KennethWang1/snakez80/loader/rom.hpp

PROGMEM const char FULL_CODE[1340] = "\x31\0\x08\xc3\xd7\x03\0\0\0\0\0\0\0\0\0\0\0\0\0\0\0\0\0\0\0\0\0\0\0\0\0\0\0\0\0\0\0\0\0\0\0\0\0\0\0\0\0\0\0\0\0\0\0\0\0\0\0\0\0\0\0\0\0\0\0\0\0\0\0\0\0\0\0\0\0\0\0\0\0\0\0\0\0\0\0\0\0\0\0\0\0\0\0\0\0\0\0\0\0\0\0\0\0\0\0\0\0\0\0\0\0\0\0\0\0\0\0\0\0\0\0\0\0\0\0\0\0\0\0\0\0\0\0\0\0\0\0\0\0\0\0\0\0\0\0\0\0\0\0\0\0\0\0\0\0\0\0\0\0\0\0\0\0\0\0\0\0\0\0\0\0\0\0\0\0\0\0\0\0\0\0\0\0\0\0\0\0\0\0\0\0\0\0\0\0\0\0\0\0\0\0\0\0\0\0\0\0\0\0\0\0\0\0\0\0\0\0\0\0\0\0\0\0\0\0\0\0\0\0\0\0\0\0\0\0\0\0\0\0\0\0\0\0\0\0\0\0\0\0\0\0\0\0\0\0\0\0\0\0\0\0\0\0\0\0\0\0\0\x21\0\x80\x4e\xaf\xb9\x17\x6f\xc9\x2a\x01\x80\xc9\xdd\xe5\xdd\x21\0\0\xdd\x39\x21\0\x80\xdd\x7e\x04\x77\xdd\xe1\xc9\x21\x01\x80\x36\0\xc9\xdd\xe5\xdd\x21\0\0\xdd\x39\x21\x07\x80\xdd\x7e\x04\x77\xdd\xe1\xc9\x2a\x32\x04\x5d\x54\xaf\xcb\x3c\xcb\x1d\x1f\x65\x6f\xeb\x7d\xab\x47\x7c\xaa\x4f\xcb\x3f\x5f\x78\xab\x6f\x61\x29\x29\x29\xad\x6f\x79\xac\x67\x22\x32\x04\xc9\x76\xc9\xdd\xe5\xdd\x21\0\0\xdd\x39\x21\xf2\xff\x39\xf9\x06\x80\x21\x0c\0\xaf\x77\x23\x77\x23\x10\xf9\x3a\x39\x04\x06\0\xdd\x77\xfe\xdd\x70\xff\x21\x3a\x04\x86\xdd\x77\xfc\x78\x23\x8e\xdd\x77\xfd\xdd\x7e\xfe\xdd\x96\xfc\xdd\x7e\xff\xdd\x9e\xfd\xe2\xae\x01\xee\x80\xf2\xd6\x01\xdd\x6e\xfe\x26\0\x11\x3c\x04\x19\x6e\x26\0\x11\x0c\0\x19\x7e\xb7\x28\x05\x3e\x01\x32\x35\x04\x36\x02\xdd\x34\xfe\x20\xcc\xdd\x34\xff\x18\xc7\x0e\0\x79\x21\x34\x04\x96\x30\x12\x06\0\x21\x06\0\x09\x6e\x26\0\x11\x0c\0\x19\x36\x03\x0c\x18\xe7\x21\x35\x04\xcb\x46\xca\x7d\x02\xdd\x36\xf2\xc1\xdd\x36\xf3\xce\xdd\x36\xf4\xaa\xdd\x36\xf5\xa8\xdd\x36\xf6\xa2\xdd\x36\xf7\xac\xdd\x36\xf8\xaa\xdd\x36\xf9\xa8\xdd\x36\xfa\xc1\xdd\x36\xfb\xce\x01\0\0\x79\xd6\x05\x30\x54\x69\x60\x29\xeb\x21\0\0\x39\x19\x7e\xdd\x77\xfc\x23\x7e\xdd\x77\xfd\x21\x06\0\x09\x29\x29\x29\x29\xdd\x75\xfe\xdd\x74\xff\x11\0\0\x7b\xd6\x10\x30\x29\x6b\x3e\x0f\x95\xdd\x6e\xfc\xdd\x66\xfd\x3c\x18\x04\xcb\x3c\xcb\x1d\x3d\x20\xf9\xcb\x45\x28\x0e\xdd\x7e\xfe\xb3\x62\xc6\x0c\x6f\x7c\xce\0\x67\x36\x01\x13\x18\xd2\x03\x18\xa7\x01\0\0\x78\xd6\x01\x30\x0b\x21\x0c\0\x09\x7e\x32\0\x80\x03\x18\xf0\xdd\xf9\xdd\xe1\xc9\x3a\0\x80\xb7\x28\x57\x3a\x37\x04\xd6\x02\x20\x04\x21\x37\x04\x35\x3a\x37\x04\x4f\xaf\x91\x30\x19\x06\0\x21\x0a\0\x09\x79\x3d\x47\x07\x9f\x57\x78\xc6\x0a\x5f\x7a\xce\0\x57\x1a\x77\x0d\x18\xe3\x21\x37\x04\x34\x3a\x01\x80\xe6\x03\x6f\x26\0\x11\x2d\x04\x19\x7e\x32\x0a\0\x4f\x07\x9f\x47\x21\x32\x04\x7e\xa9\x77\x23\x7e\xa8\x77\xcd\x43\x01\xcd\x43\x01\xc3\x43\x01\xc9\xdd\xe5\xdd\x21\0\0\xdd\x39\xf5\xf5\x21\x37\x04\x7e\xb7\x28\x25\x4e\x0d\x71\x06\0\x21\x0a\0\x09\x4e\x3a\x36\x04\x47\x07\x9f\x57\xaf\x90\x5f\x9f\x92\x57\x79\x6f\x07\x9f\x67\xaf\xed\x52\x28\x04\x21\x36\x04\x71\x01\x3c\x04\x2a\x39\x04\x26\0\x09\x66\x3a\x36\x04\x6f\xeb\x07\x9f\x6f\x7a\x26\0\x83\xdd\x77\xfc\x7c\x8d\xdd\x77\xfd\x3a\x36\x04\xdd\x5e\xfc\x0f\x30\x1a\x6b\xcb\x3d\xcb\x3d\xcb\x3d\xcb\x3d\x7a\x07\x07\x07\x07\xe6\x0f\x95\x28\x12\x21\x35\x04\x36\x01\x18\x0b\xdd\x7e\xfd\xb7\x28\x05\x21\x35\x04\x36\x01\x21\x35\x04\xcb\x46\x20\x56\x21\x39\x04\x35\x79\x86\x4f\x30\x01\x04\x7b\x02\x01\0\0\x3a\x34\x04\x5f\x16\0\x79\x93\x78\x9a\xe2\x9a\x03\xee\x80\xf2\xd2\x03\x21\x06\0\x09\xdd\x75\xfe\xdd\x74\xff\x5e\x16\0\xe1\xe5\xaf\xed\x52\x20\x1e\x2a\x3a\x04\x23\x22\x3a\x04\xc5\xcd\x43\x01\xeb\xc1\x16\0\x21\x0c\0\x19\x7e\xb7\x20\xf0\xdd\x6e\xfe\xdd\x66\xff\x73\x03\x18\xb9\xdd\xf9\xdd\xe1\xc9\x06\x80\x21\x0c\0\xaf\x77\x23\x77\x23\x10\xf9\x01\0\0\x3a\x34\x04\x5f\x16\0\x79\x93\x78\x9a\xe2\xf5\x03\xee\x80\xf2\x08\x04\x21\x06\0\x09\xe5\xc5\xcd\x43\x01\xeb\xc1\xe1\x73\x03\x18\xde\xcd\x95\x02\x21\x35\x04\xcb\x46\x20\x11\x21\x38\x04\x7e\x3c\x77\xd6\x03\x20\x07\xaf\x32\x38\x04\xcd\xf3\x02\xcd\x6c\x01\x21\x01\x80\x36\0\x18\xdb\xff\x10\x01\xf0\x03\x63\x9f\x02\0\x01\0\0\0\x03\0\x13\x12\x11\0\0\0\0\0\0\0\0\0\0\0\0\0\0\0\0\0\0\0\0\0\0\0\0\0\0\0\0\0\0\0\0\0\0\0\0\0\0\0\0\0\0\0\0\0\0\0\0\0\0\0\0\0\0\0\0\0\0\0\0\0\0\0\0\0\0\0\0\0\0\0\0\0\0\0\0\0\0\0\0\0\0\0\0\0\0\0\0\0\0\0\0\0\0\0\0\0\0\0\0\0\0\0\0\0\0\0\0\0\0\0\0\0\0\0\0\0\0\0\0\0\0\0\0\0\0\0\0\0\0\0\0\0\0\0\0\0\0\0\0\0\0\0\0\0\0\0\0\0\0\0\0\0\0\0\0\0\0\0\0\0\0\0\0\0\0\0\0\0\0\0\0\0\0\0\0\0\0\0\0\0\0\0\0\0\0\0\0\0\0\0\0\0\0\0\0\0\0\0\0\0\0\0\0\0\0\0\0\0\0\0\0\0\0\0\0\0\0\0\0\0\0\0\0\0\0\0\0\0\0\0\0\0\0\0\0\0\0\0\0\0\0\0\0\0\0\0\0\0\0\0\0\0";
